Cocotrilito/Voyager-Panel/images/aliexpress cart.png

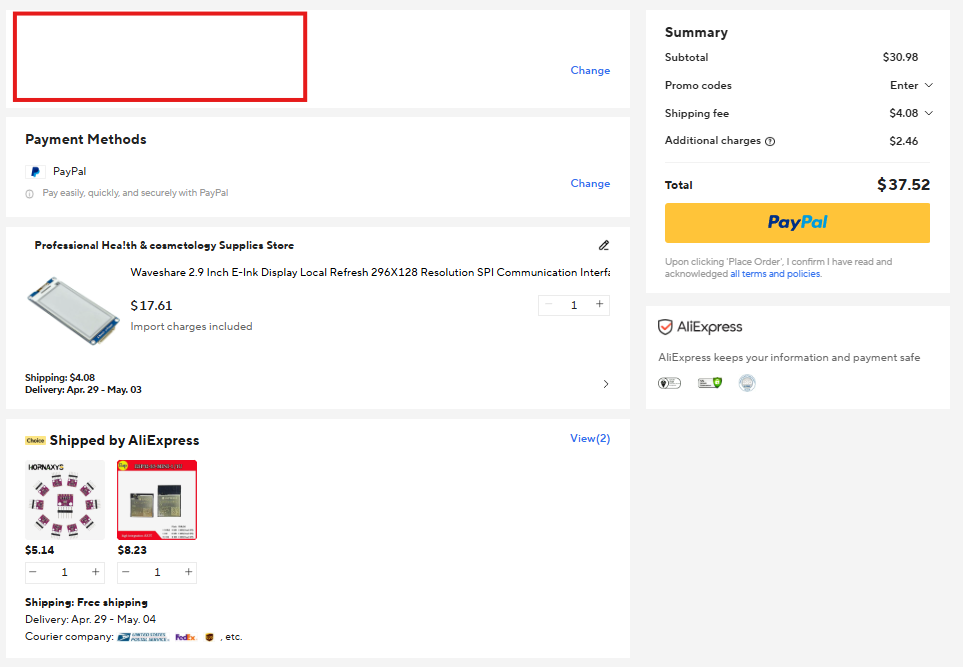
images/aliexpress cart.png
