Cocotrilito/Voyager-Panel/images/CASE CAD.png

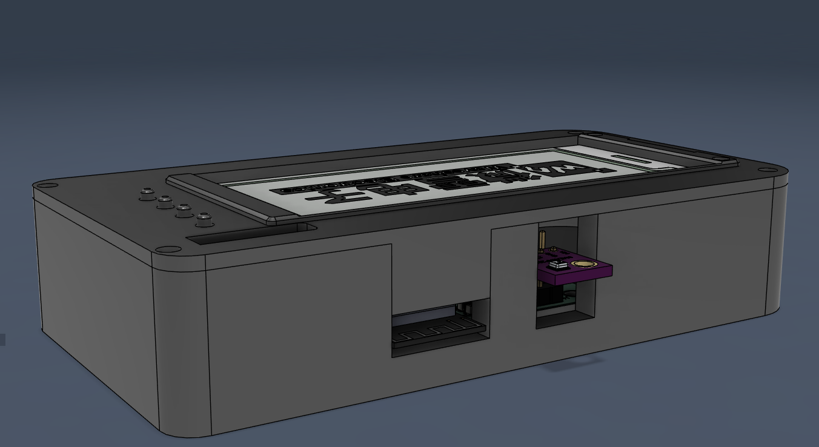
images/CASE CAD.png
