Cocotrilito/Voyager-Panel/images/front.png

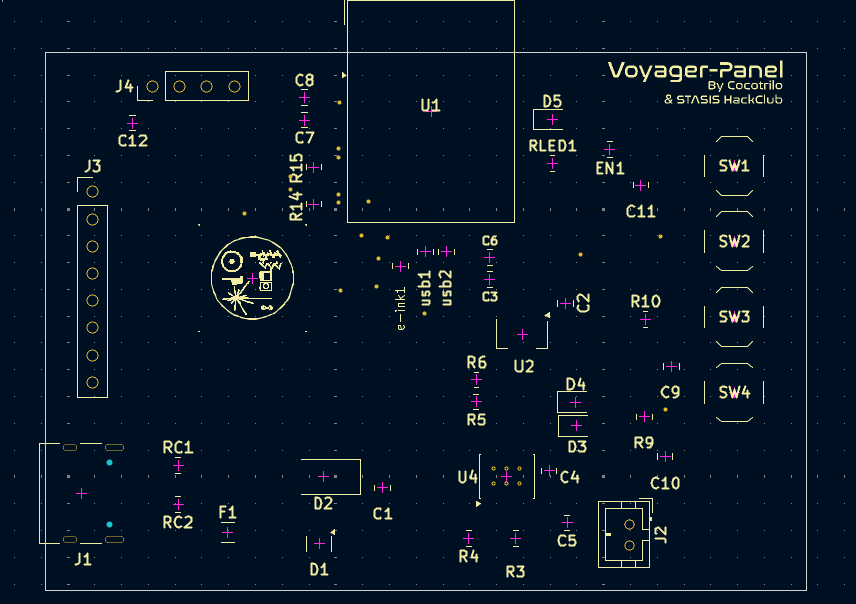
images/front.png
