Cocotrilito/Voyager-Panel/images/JLCPCB cart.png

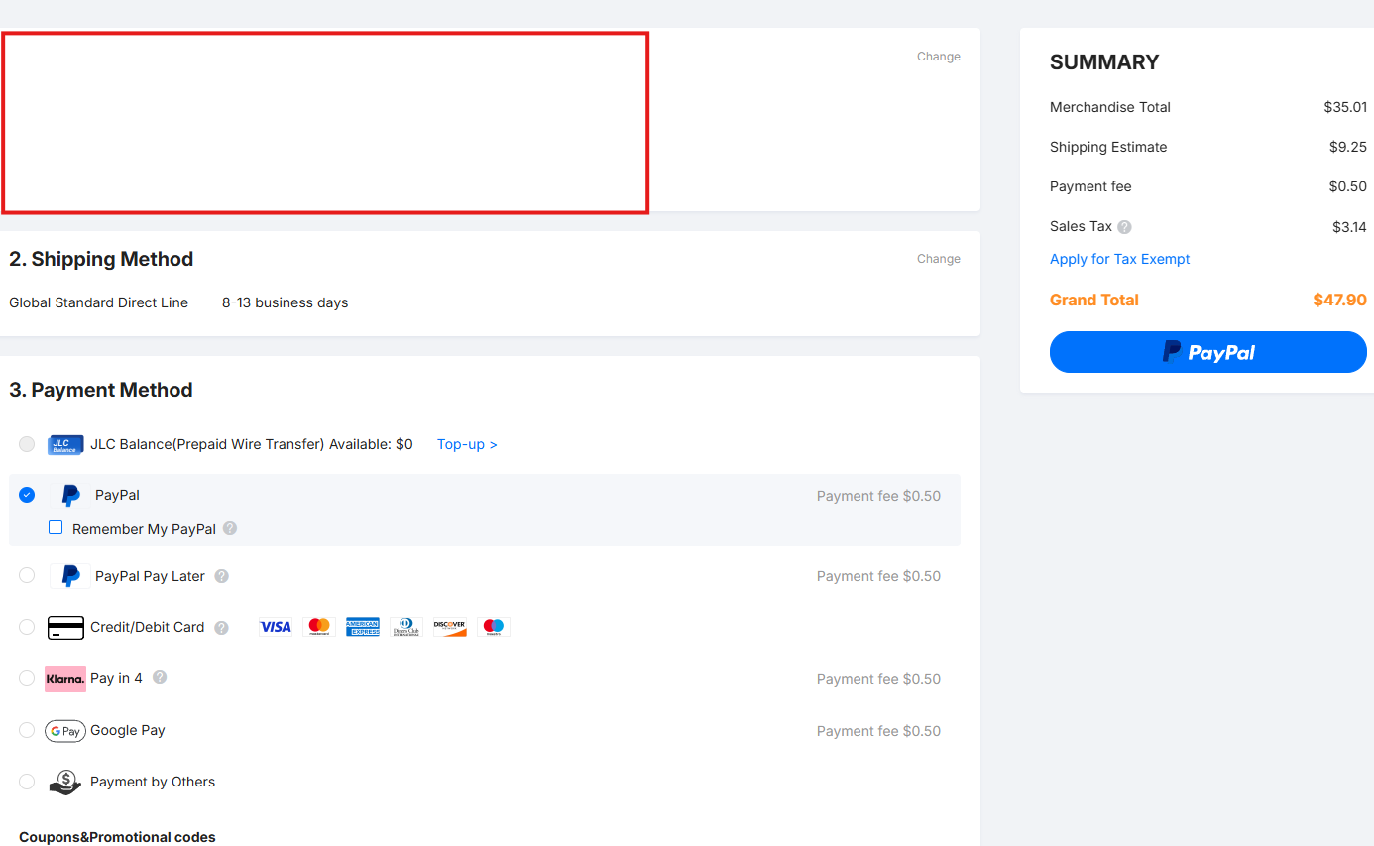
images/JLCPCB cart.png
