Cocotrilito/Voyager-Panel/images/pattern test 1.jpg

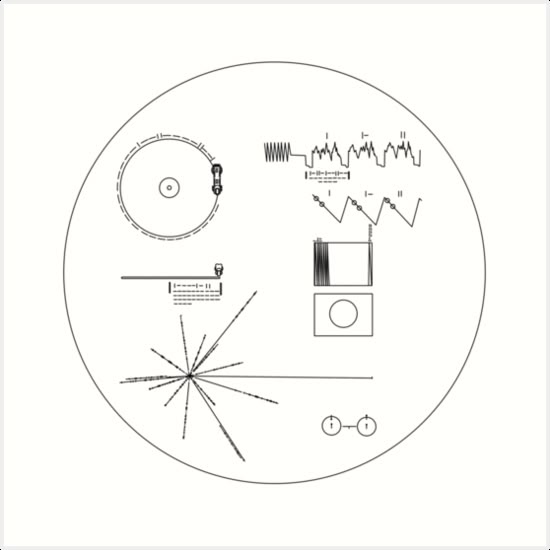
images/pattern test 1.jpg
