Cocotrilito/Voyager-Panel/images/pattern test 2.jpg

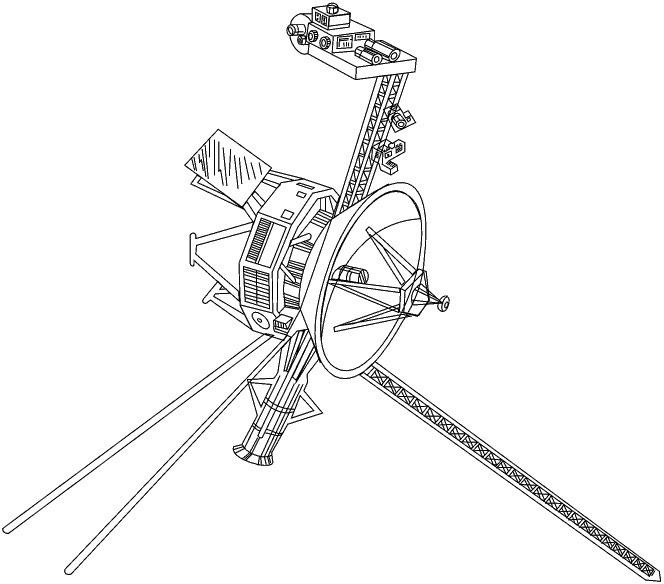
images/pattern test 2.jpg
