Cocotrilito/Voyager-Panel/firmware/final build/VoyagerPanelFirmware/src/images.h

#ifndef IMAGES_H
#define IMAGES_H
#include <Arduino.h>

// 'A_large_blank_world_map_with_oceans_marked_in_blue-edited', 296x128px
const unsigned char world_map_bitmap [] PROGMEM = {
	0xb6, 0xdb, 0x6d, 0xb6, 0xdb, 0x6d, 0xb6, 0xdb, 0x6d, 0xb6, 0xdb, 0x6d, 0xb6, 0xdb, 0x6d, 0xb6, 
	0xdb, 0x6d, 0xb6, 0xdb, 0x6d, 0xb6, 0xdb, 0x6d, 0xb6, 0xdb, 0x6d, 0xb6, 0xdb, 0x6d, 0xb6, 0xdb, 
	0x6d, 0xb6, 0xdb, 0x6d, 0xb6, 0x93, 0x26, 0x4c, 0x99, 0x32, 0x64, 0xc9, 0x93, 0x26, 0x4c, 0x99, 
	0x32, 0x64, 0xc9, 0x93, 0x26, 0x4c, 0x99, 0x32, 0x64, 0xc9, 0x93, 0x26, 0x4c, 0x99, 0x32, 0x64, 
	0xc9, 0x93, 0x26, 0x4c, 0x99, 0x32, 0x64, 0xc9, 0x93, 0x24, 0xd9, 0xb5, 0xb3, 0x6d, 0xad, 0x9b, 
	0x6d, 0x6c, 0xdb, 0x6b, 0xed, 0xdb, 0x7f, 0x3e, 0xda, 0xd9, 0xb6, 0xd6, 0xcd, 0xb6, 0xb6, 0x6d, 
	0xb5, 0xb3, 0x6d, 0xad, 0x9b, 0x6d, 0x6c, 0xdb, 0x6b, 0x66, 0xdb, 0x5b, 0x36, 0xda, 0xdb, 0x6c, 
	0xd9, 0xb6, 0x66, 0xcd, 0xb3, 0x36, 0x6d, 0x99, 0xb2, 0x03, 0xc8, 0x80, 0x02, 0x6c, 0xdb, 0x33, 
	0x66, 0xdd, 0xbf, 0x36, 0xcc, 0xd9, 0xb6, 0x66, 0xcd, 0xb3, 0x36, 0x6d, 0x99, 0xb3, 0x6c, 0xcd, 
	0x9b, 0x66, 0x6c, 0xdb, 0x27, 0x4e, 0x4d, 0x9a, 0x72, 0x6c, 0xd3, 0x93, 0x6e, 0x34, 0xfa, 0x00, 
	0x00, 0x80, 0xcd, 0x26, 0xdb, 0x3b, 0x33, 0x49, 0xc9, 0xb3, 0x8e, 0x4d, 0x9a, 0x72, 0x6c, 0xd3, 
	0x93, 0x66, 0x9c, 0x9b, 0x34, 0xe4, 0xd9, 0xa7, 0x24, 0xd9, 0x66, 0xd9, 0xb3, 0x36, 0xcd, 0x9a, 
	0xfd, 0xba, 0xe3, 0x88, 0x12, 0x48, 0x25, 0xb3, 0xb4, 0xe9, 0xc9, 0xac, 0xda, 0x6e, 0x6e, 0x73, 
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
	0x81, 0xc2, 0x40, 0x41, 0x30, 0x88, 0x01, 0x00, 0x24, 0x40, 0xc0, 0x84, 0x42, 0x24, 0x80, 0x97, 
	0x6c, 0xdb, 0x33, 0x66, 0xd9, 0xc8, 0x01, 0x0a, 0x04, 0x21, 0xe1, 0x24, 0xdc, 0xe1, 0xdb, 0x37, 
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
};

#endif
